ngteq/T-Modem/docs/images/explode/t-modem-explode-02-pico.png

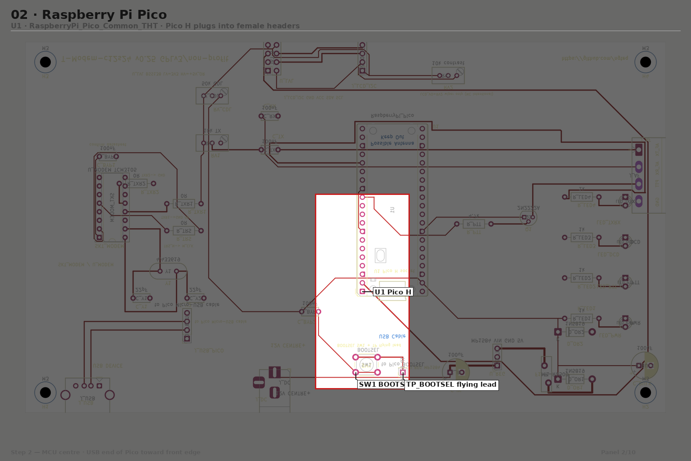
docs/images/explode/t-modem-explode-02-pico.png
