ngteq/T-Modem/docs/images/explode/t-modem-explode-04-crystal.png

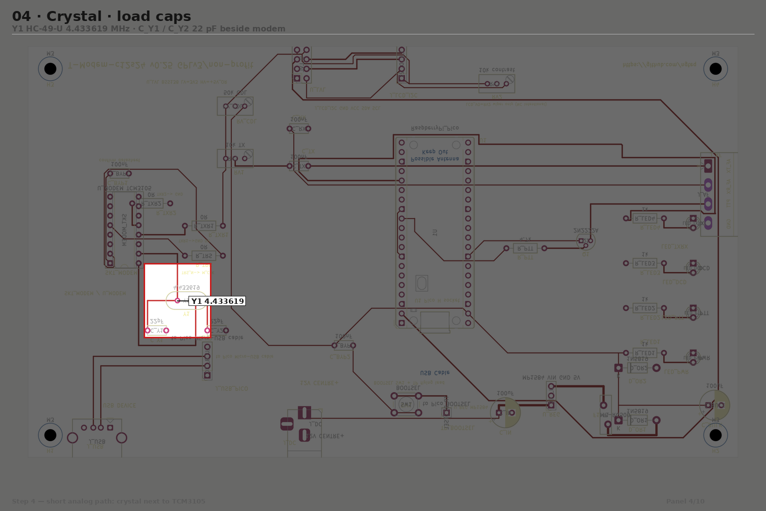
docs/images/explode/t-modem-explode-04-crystal.png
