ngteq/T-Modem/docs/images/explode/t-modem-explode-08-straps-leds.png

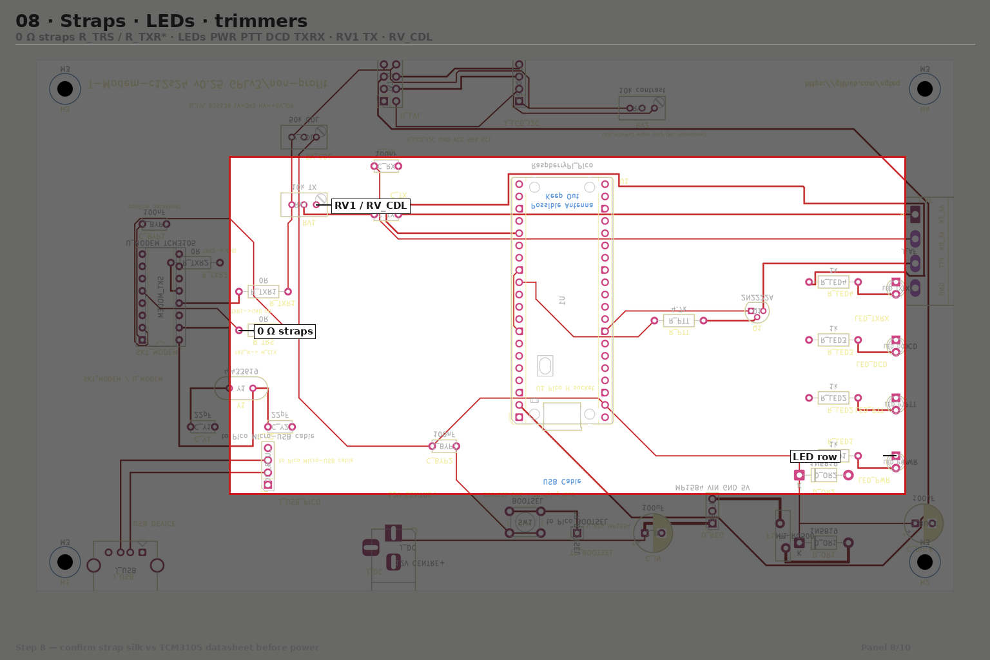
docs/images/explode/t-modem-explode-08-straps-leds.png
