ngteq/T-Modem/docs/images/explode/t-modem-explode-10-complete-stack.png

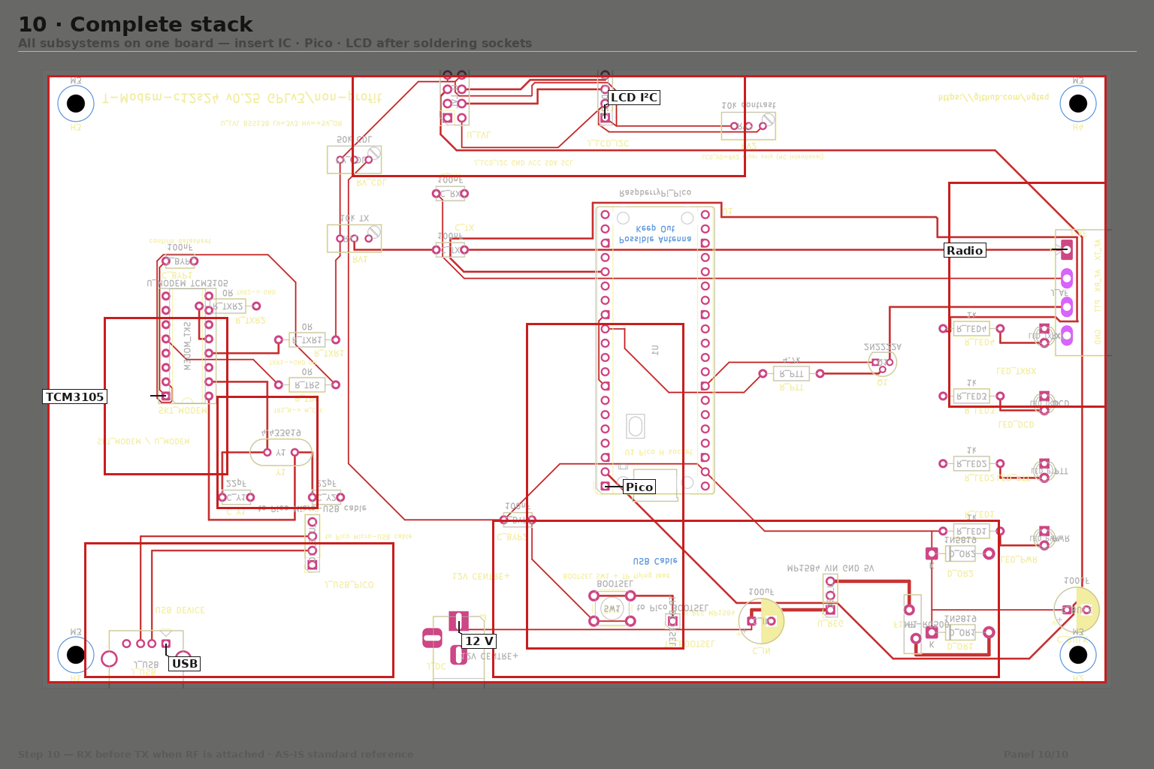
docs/images/explode/t-modem-explode-10-complete-stack.png
